JeremySavonet/Eurobot-2016_The-beach-bots/meca/10 telemetre laser/10.04 supp miroir.SLDPRT

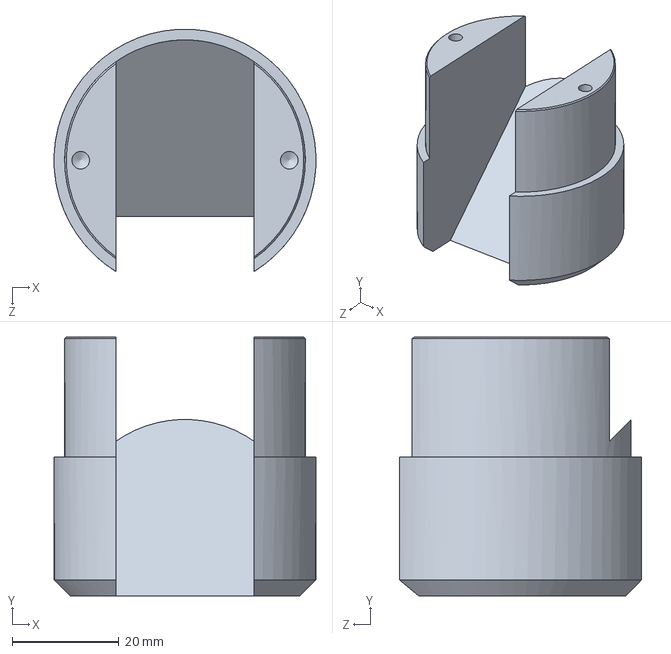
[picture p28: CAD file, 2015-11-07]
meca/10 telemetre laser/10.04 supp miroir.SLDPRT
49.0 x 48.4 x 45.3 mm
