JeremySavonet/Eurobot-2016_The-beach-bots/meca/12 bras/12.33 rot pince.SLDPRT

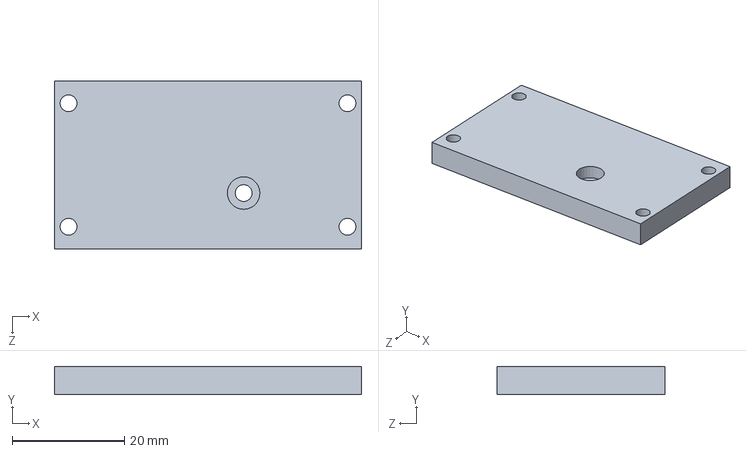
[picture p29: CAD file, 2015-11-07]
meca/12 bras/12.33 rot pince.SLDPRT
54.7 x 5.00 x 30.0 mm
