JeremySavonet/Eurobot-2016_The-beach-bots/meca/10 telemetre laser/10.06 poulie entrainement telemetre.SLDPRT

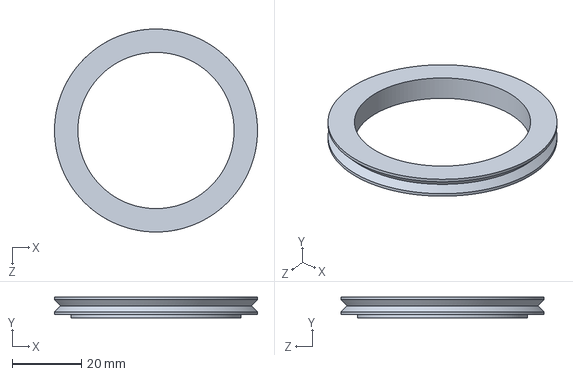
[picture p30: CAD file, 2015-11-07]
meca/10 telemetre laser/10.06 poulie entrainement telemetre.SLDPRT
58.5 x 6.00 x 58.5 mm
