JeremySavonet/Eurobot-2016_The-beach-bots/meca/22.01 telemetre.SLDPRT

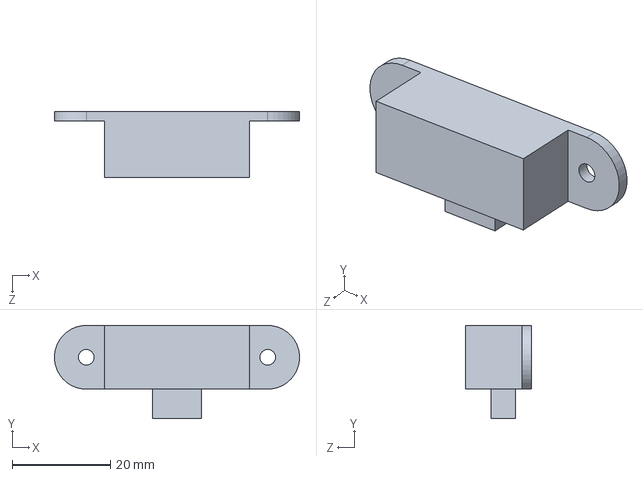
[picture p32: CAD file, 2015-11-07]
meca/22.01 telemetre.SLDPRT
50.0 x 19.0 x 13.5 mm
