JeremySavonet/Eurobot-2016_The-beach-bots/meca/04.02 supp servo telemetres.SLDPRT

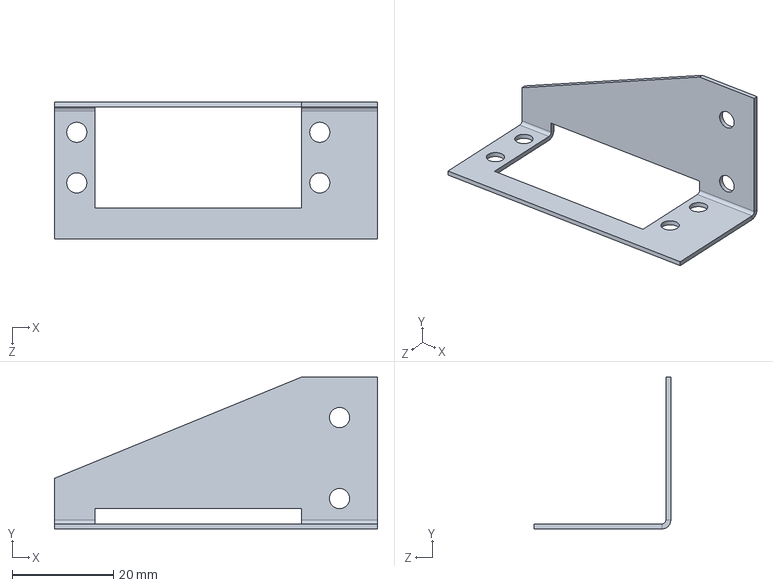
[picture p33: CAD file, 2015-11-07]
meca/04.02 supp servo telemetres.SLDPRT
63.8 x 30.0 x 27.0 mm
