JeremySavonet/Eurobot-2016_The-beach-bots/meca/10 telemetre laser/10.02 supp vertical telemetre.SLDPRT

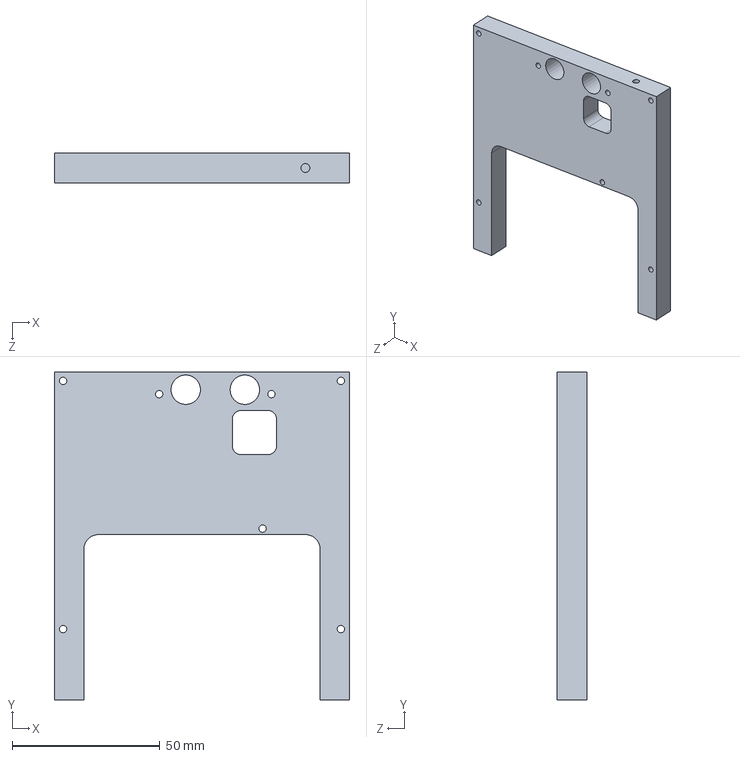
[picture p34: CAD file, 2015-11-07]
meca/10 telemetre laser/10.02 supp vertical telemetre.SLDPRT
100.0 x 111.0 x 10.0 mm
