JeremySavonet/Eurobot-2016_The-beach-bots/meca/04.01 supp telemetres.SLDPRT

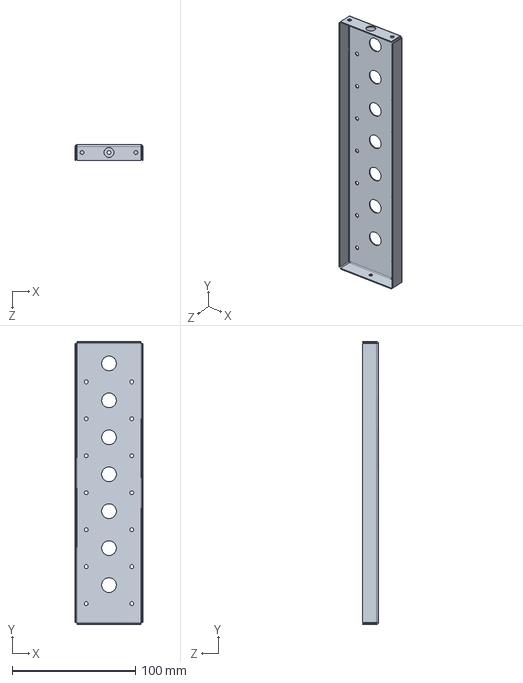
[picture p36: CAD file, 2015-11-07]
meca/04.01 supp telemetres.SLDPRT
55.0 x 229.8 x 12.8 mm
