JeremySavonet/Eurobot-2016_The-beach-bots/meca/10 telemetre laser/10.01 supp dessous telemetre.SLDPRT

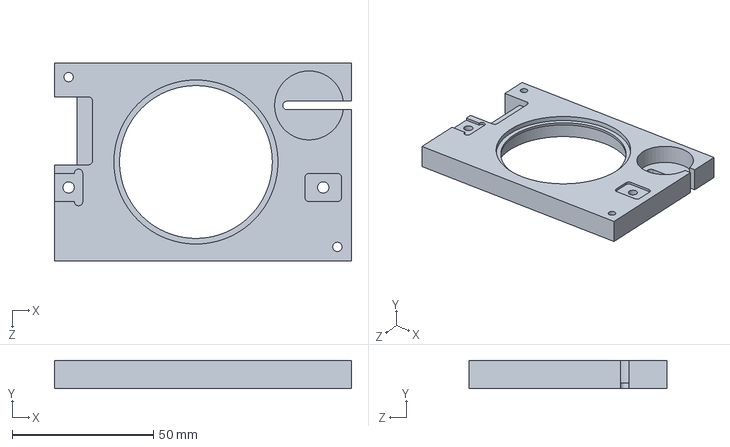
[picture p37: CAD file, 2015-11-07]
meca/10 telemetre laser/10.01 supp dessous telemetre.SLDPRT
105.0 x 10.0 x 70.0 mm
