JeremySavonet/Eurobot-2016_The-beach-bots/meca/12 bras/servo moteur MG995.SLDPRT

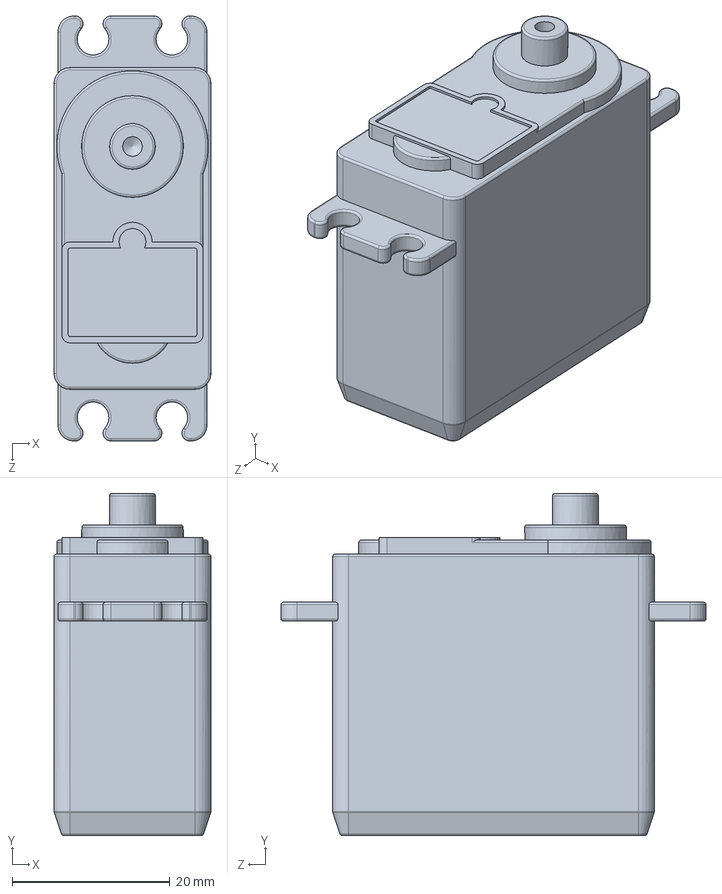
[picture p38: CAD file, 2015-11-07]
meca/12 bras/servo moteur MG995.SLDPRT
19.9 x 43.4 x 53.9 mm
