JeremySavonet/Eurobot-2016_The-beach-bots/meca/12 bras/vis - chcm4 - 39.sldprt

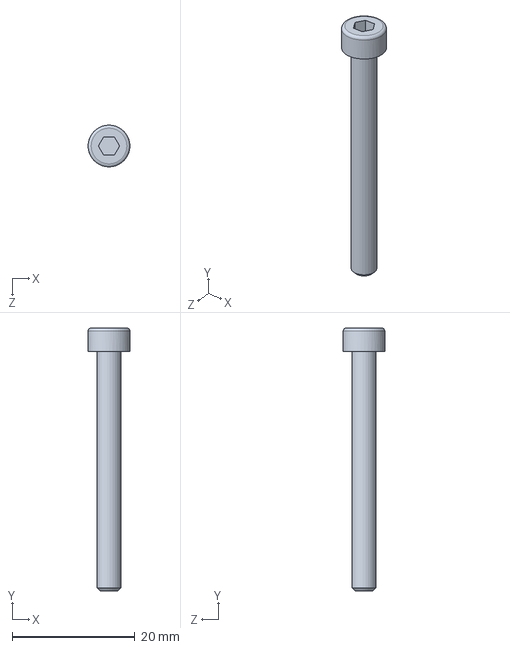
[picture p39: CAD file, 2015-11-07]
meca/12 bras/vis - chcm4 - 39.sldprt
6.80 x 42.8 x 6.80 mm
