JeremySavonet/Eurobot-2016_The-beach-bots/meca/03.04 supp codeurs.SLDPRT

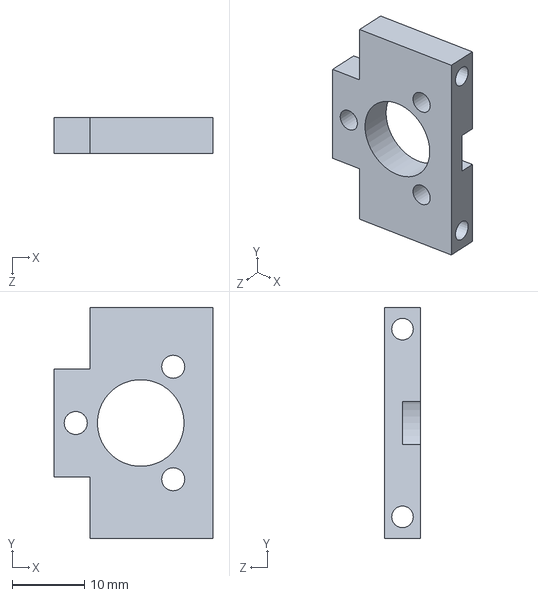
[picture p40: CAD file, 2015-11-07]
meca/03.04 supp codeurs.SLDPRT
22.0 x 32.0 x 5.00 mm
