JeremySavonet/Eurobot-2016_The-beach-bots/meca/10 telemetre laser/10.13 fentes led.SLDPRT

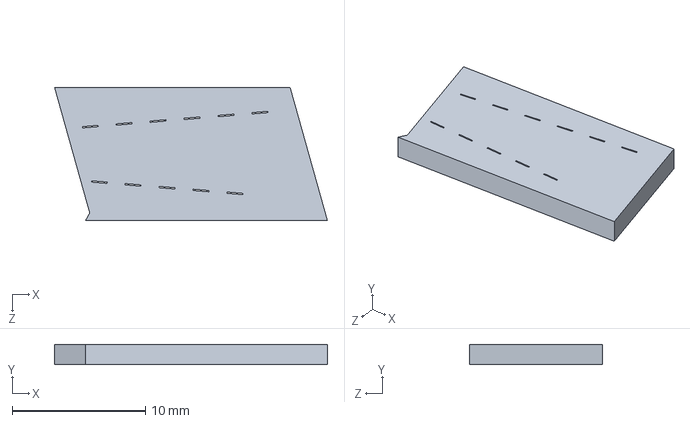
[picture p41: CAD file, 2015-11-07]
meca/10 telemetre laser/10.13 fentes led.SLDPRT
20.5 x 1.50 x 10.0 mm
