JeremySavonet/Eurobot-2016_The-beach-bots/meca/12 bras/12.12 rot bras.SLDPRT

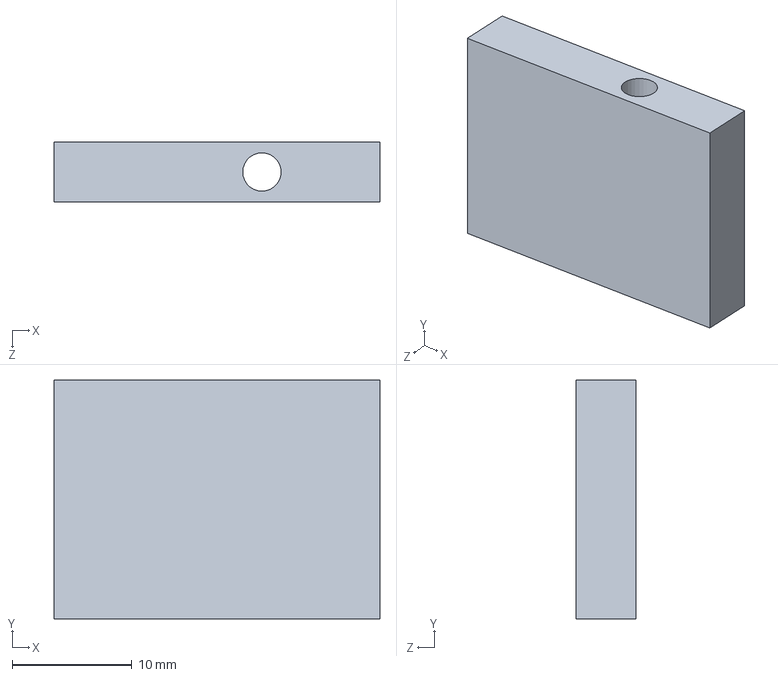
[picture p42: CAD file, 2015-11-07]
meca/12 bras/12.12 rot bras.SLDPRT
27.2 x 19.9 x 5.00 mm
