JeremySavonet/Eurobot-2016_The-beach-bots/meca/10 telemetre laser/10.03 supp fourche optique.SLDPRT

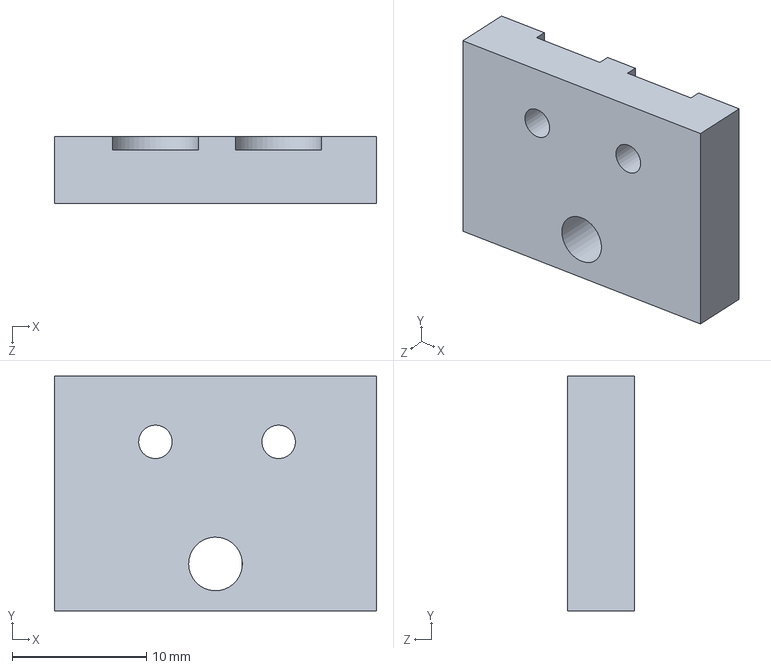
[picture p43: CAD file, 2015-11-07]
meca/10 telemetre laser/10.03 supp fourche optique.SLDPRT
24.0 x 17.5 x 5.00 mm
