JeremySavonet/Eurobot-2016_The-beach-bots/meca/12 bras/12.51 pince.SLDPRT

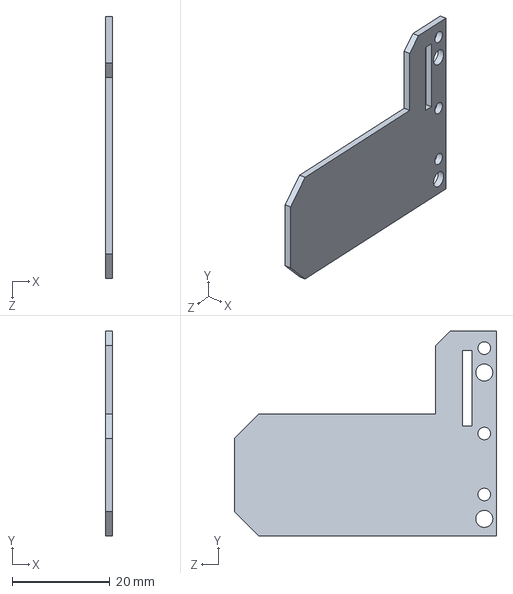
[picture p44: CAD file, 2015-11-07]
meca/12 bras/12.51 pince.SLDPRT
1.50 x 42.0 x 53.7 mm
