JeremySavonet/Eurobot-2016_The-beach-bots/meca/21.04 int coupe tout.SLDPRT

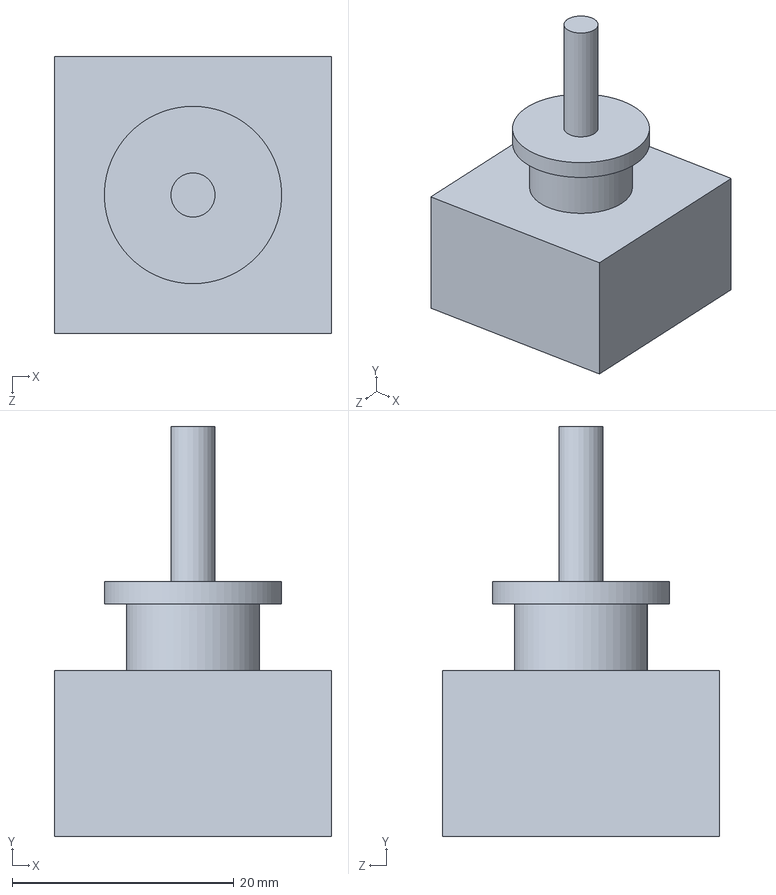
[picture p45: CAD file, 2015-11-07]
meca/21.04 int coupe tout.SLDPRT
25.0 x 37.0 x 25.0 mm
