JeremySavonet/Eurobot-2016_The-beach-bots/meca/03.01 codeurs.SLDPRT

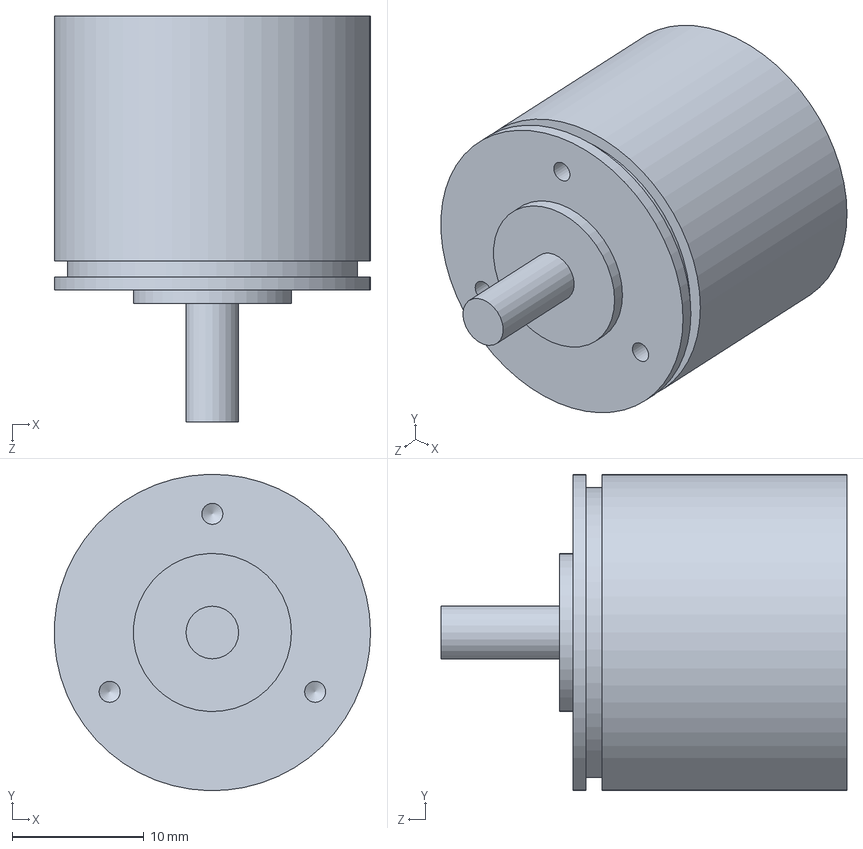
[picture p46: CAD file, 2015-11-07]
meca/03.01 codeurs.SLDPRT
24.0 x 24.0 x 30.8 mm
