JeremySavonet/Eurobot-2016_The-beach-bots/meca/10 telemetre laser/10.00 telemetre laser.SLDPRT

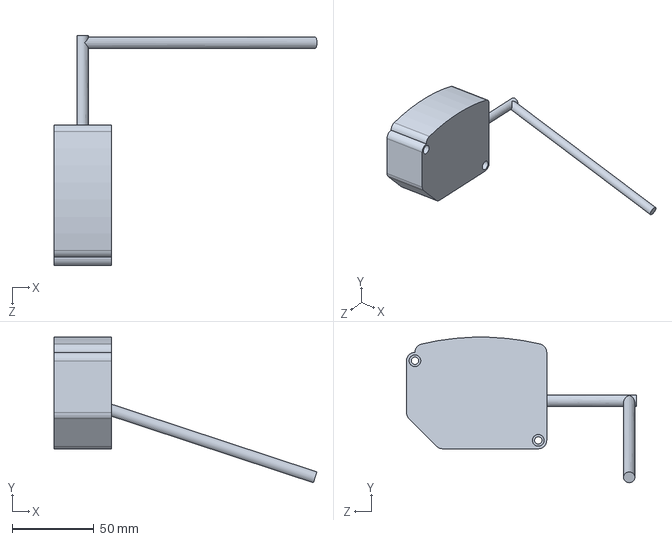
[picture p47: CAD file, 2015-11-07]
meca/10 telemetre laser/10.00 telemetre laser.SLDPRT
161.2 x 89.2 x 141.0 mm
