JeremySavonet/Eurobot-2016_The-beach-bots/meca/12 bras/12.34 rot pince.SLDPRT

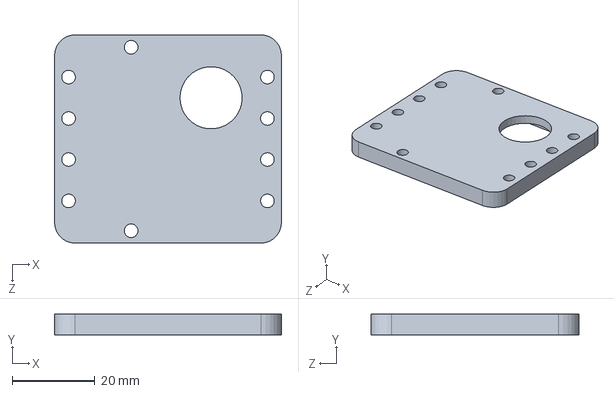
[picture p48: CAD file, 2015-11-07]
meca/12 bras/12.34 rot pince.SLDPRT
54.8 x 5.00 x 50.3 mm
