JeremySavonet/Eurobot-2016_The-beach-bots/meca/10 telemetre laser/10.00 fourche optique.SLDPRT

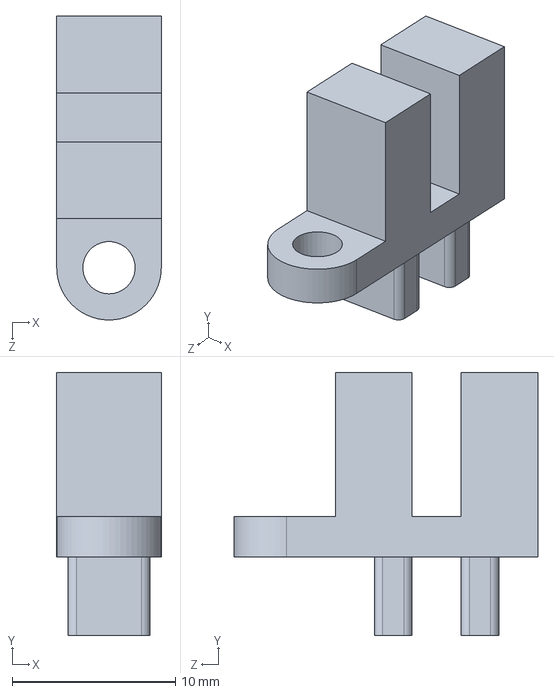
[picture p49: CAD file, 2015-11-07]
meca/10 telemetre laser/10.00 fourche optique.SLDPRT
6.40 x 16.1 x 18.6 mm
