JeremySavonet/Eurobot-2016_The-beach-bots/meca/12 bras/12.63 sup mors.SLDPRT

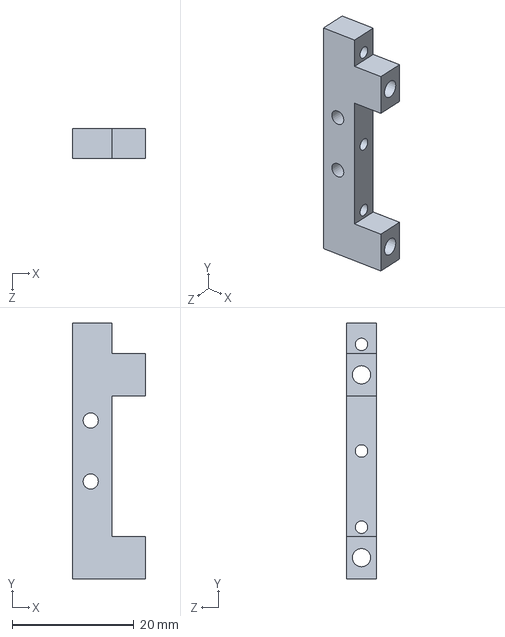
[picture p50: CAD file, 2015-11-07]
meca/12 bras/12.63 sup mors.SLDPRT
12.0 x 42.0 x 5.00 mm
