JeremySavonet/Eurobot-2016_The-beach-bots/meca/21.05 tirette.SLDPRT

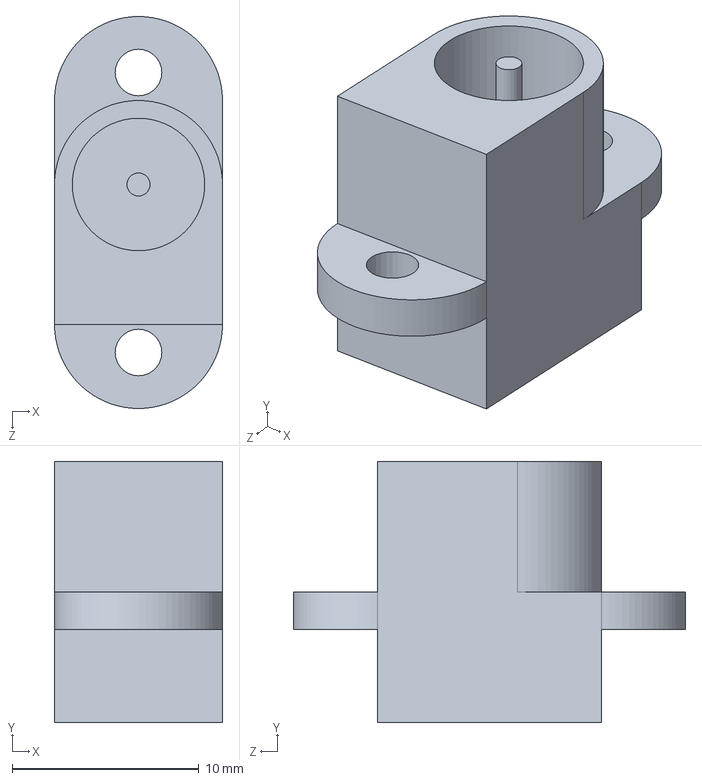
[picture p51: CAD file, 2015-11-07]
meca/21.05 tirette.SLDPRT
9.00 x 14.0 x 21.0 mm
