JeremySavonet/Eurobot-2016_The-beach-bots/meca/10 telemetre laser/10.00 roulement miroir.SLDPRT

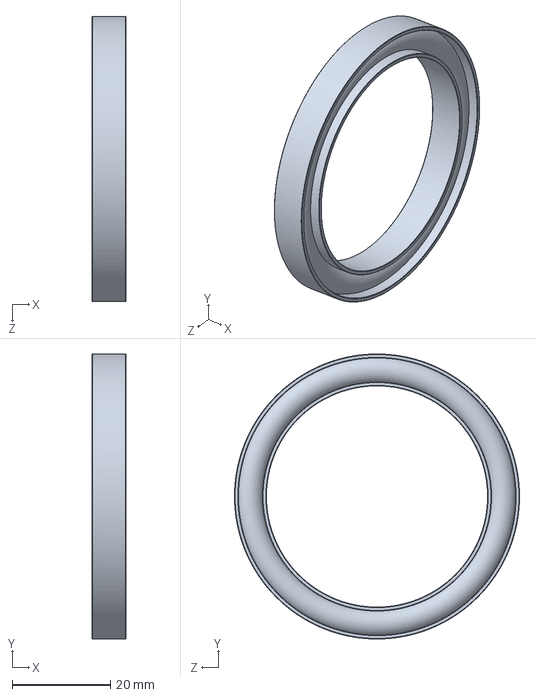
[picture p52: CAD file, 2015-11-07]
meca/10 telemetre laser/10.00 roulement miroir.SLDPRT
7.00 x 58.0 x 58.0 mm
