JeremySavonet/Eurobot-2016_The-beach-bots/meca/12 bras/12.25 bras 2.SLDPRT

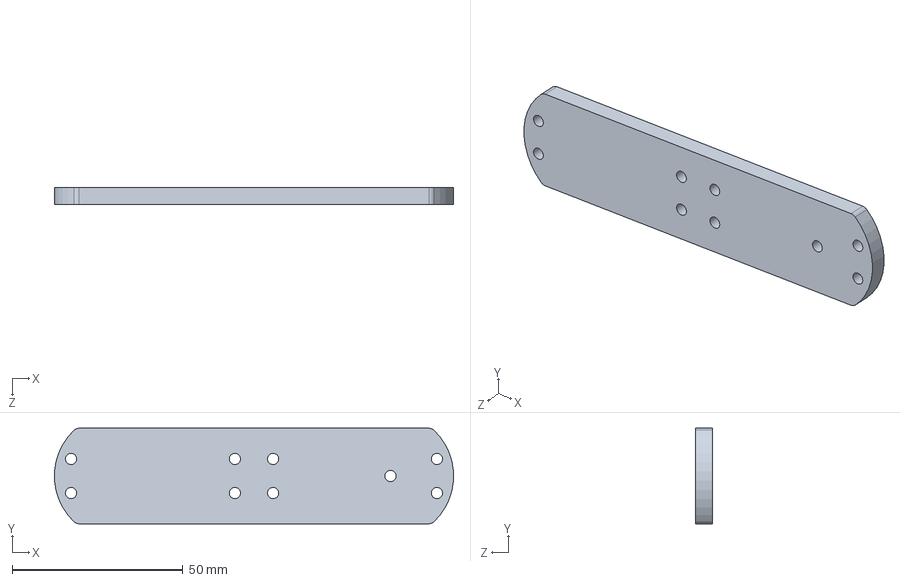
[picture p53: CAD file, 2015-11-07]
meca/12 bras/12.25 bras 2.SLDPRT
116.9 x 28.0 x 5.00 mm
