JeremySavonet/Eurobot-2016_The-beach-bots/meca/21.02 arret urgence.SLDPRT

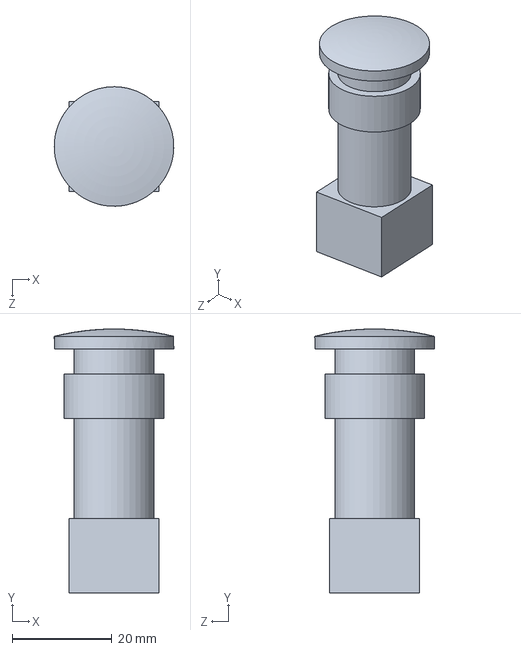
[picture p54: CAD file, 2015-11-07]
meca/21.02 arret urgence.SLDPRT
24.0 x 53.0 x 24.0 mm
