JeremySavonet/Eurobot-2016_The-beach-bots/meca/03.02 roue codeuse.SLDPRT

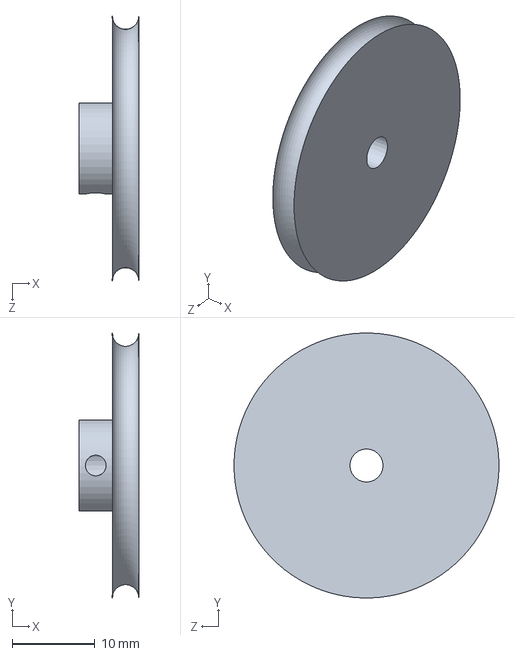
[picture p55: CAD file, 2015-11-07]
meca/03.02 roue codeuse.SLDPRT
7.20 x 32.0 x 32.0 mm
