JeremySavonet/Eurobot-2016_The-beach-bots/meca/12 bras/12.51 pince bielette.SLDPRT

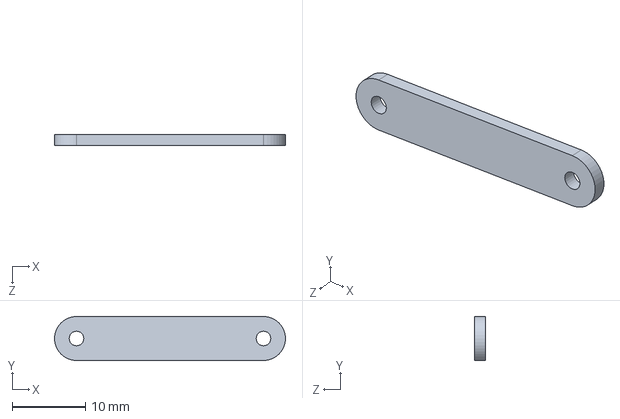
[picture p56: CAD file, 2015-11-07]
meca/12 bras/12.51 pince bielette.SLDPRT
31.5 x 6.00 x 1.50 mm
