JeremySavonet/Eurobot-2016_The-beach-bots/meca/01.01 chassis.SLDPRT

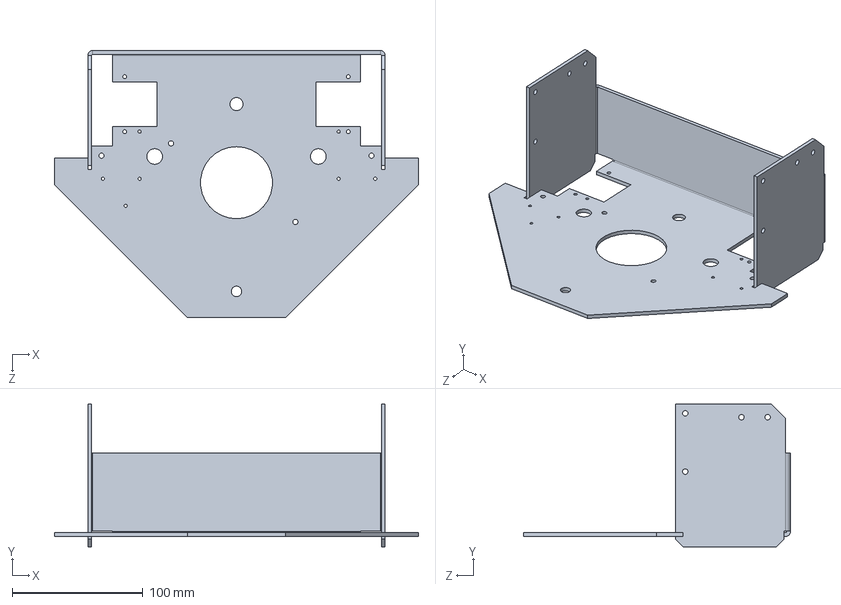
[picture p57: CAD file, 2015-11-07]
meca/01.01 chassis.SLDPRT
278.0 x 109.0 x 204.0 mm
