JeremySavonet/Eurobot-2016_The-beach-bots/meca/12 bras/12.61 tige.SLDPRT

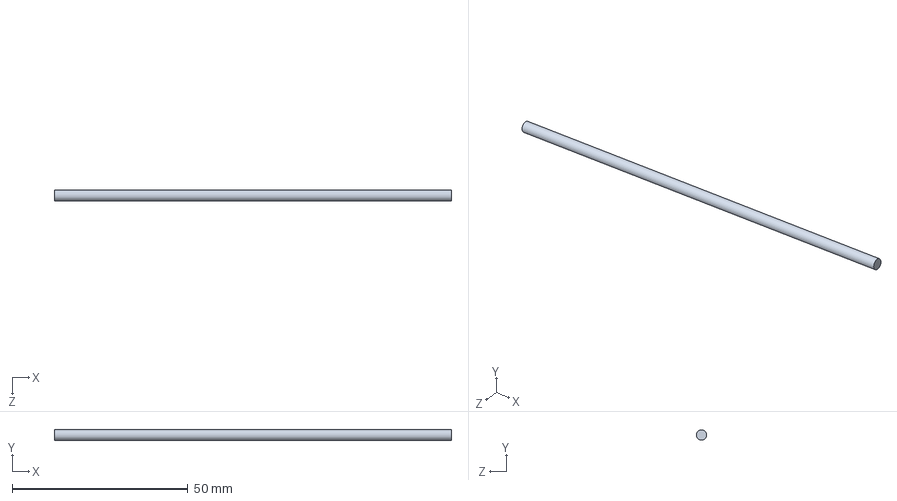
[picture p58: CAD file, 2015-11-07]
meca/12 bras/12.61 tige.SLDPRT
113.0 x 3.00 x 3.00 mm
