JeremySavonet/Eurobot-2016_The-beach-bots/meca/03.03 joint roue codeuse.SLDPRT

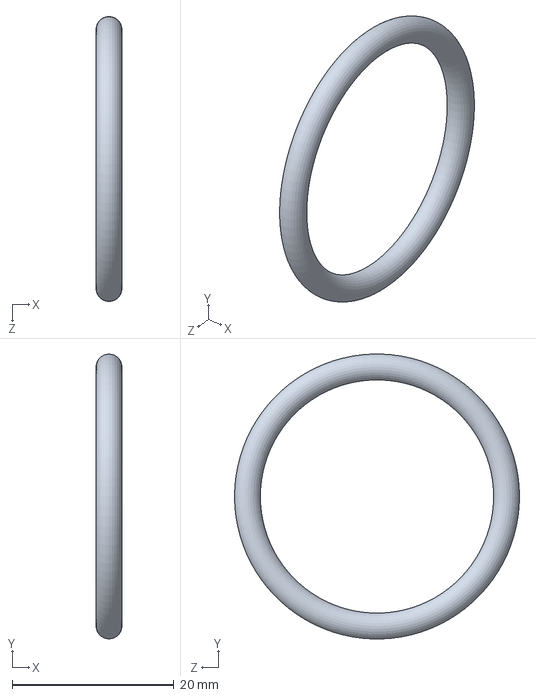
[picture p59: CAD file, 2015-11-07]
meca/03.03 joint roue codeuse.SLDPRT
3.20 x 35.2 x 35.2 mm
