JeremySavonet/Eurobot-2016_The-beach-bots/meca/12 bras/12.14 rot bras.SLDPRT

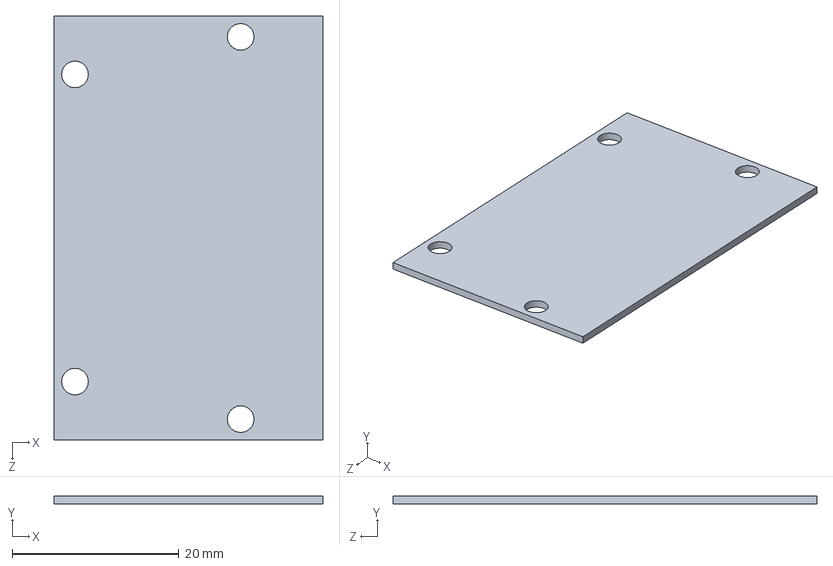
[picture p60: CAD file, 2015-11-07]
meca/12 bras/12.14 rot bras.SLDPRT
32.2 x 1.00 x 50.8 mm
