JeremySavonet/Eurobot-2016_The-beach-bots/meca/02.02 roue folle.SLDPRT

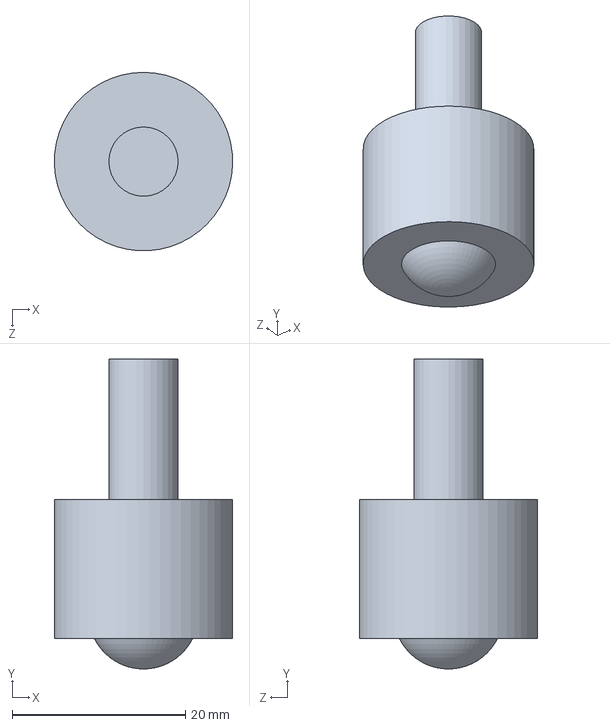
[picture p61: CAD file, 2015-11-07]
meca/02.02 roue folle.SLDPRT
20.6 x 35.8 x 20.6 mm
