JeremySavonet/Eurobot-2016_The-beach-bots/meca/12 bras/12.52 pince pile.SLDPRT

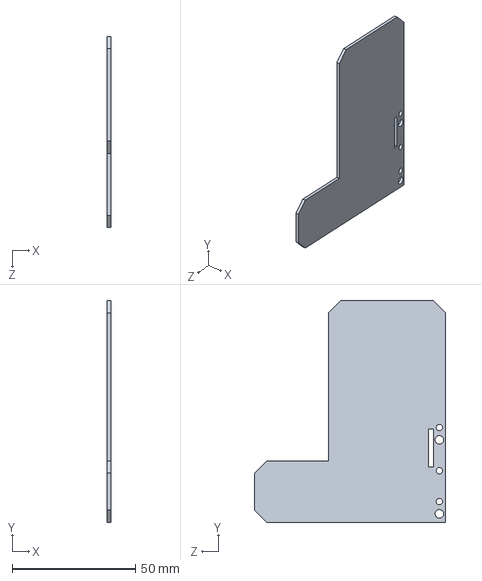
[picture p62: CAD file, 2015-11-07]
meca/12 bras/12.52 pince pile.SLDPRT
1.50 x 90.0 x 77.5 mm
