JeremySavonet/Eurobot-2016_The-beach-bots/meca/12 bras/vis - chcm3 - 6.sldprt

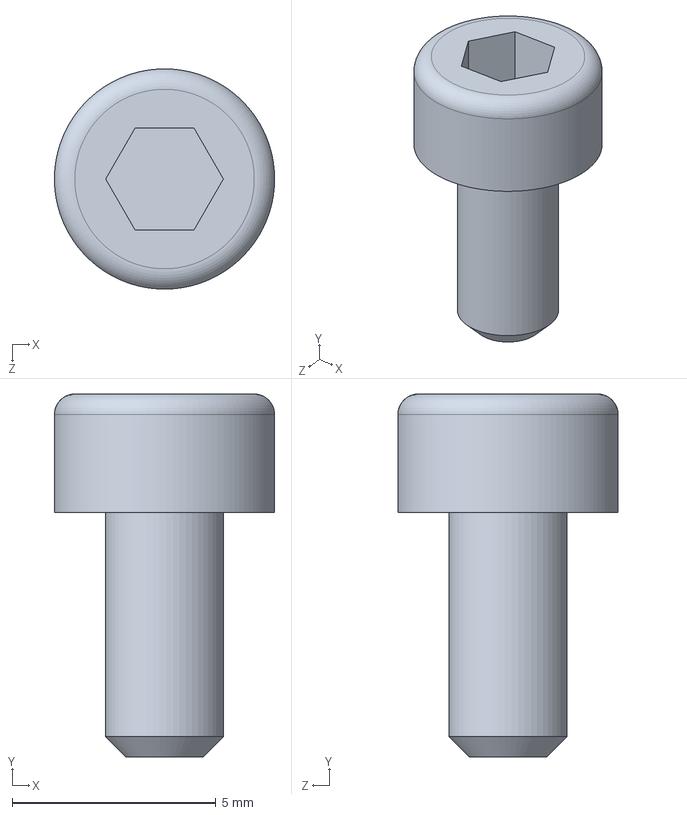
[picture p63: CAD file, 2015-11-07]
meca/12 bras/vis - chcm3 - 6.sldprt
5.40 x 8.90 x 5.40 mm
