JeremySavonet/Eurobot-2016_The-beach-bots/meca/12 bras/12.31 sup pince .SLDPRT

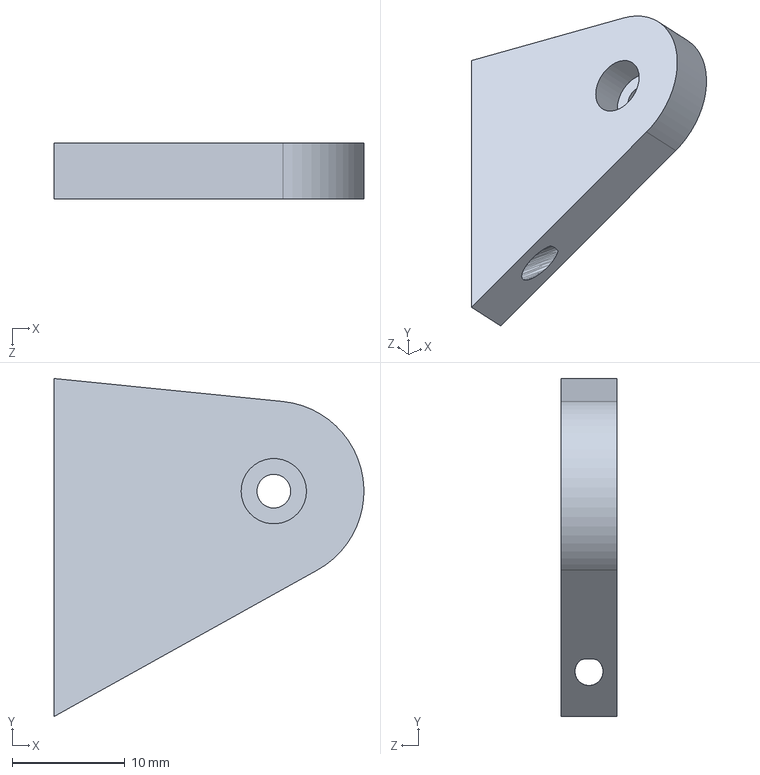
[picture p64: CAD file, 2015-11-07]
meca/12 bras/12.31 sup pince .SLDPRT
27.5 x 30.0 x 5.00 mm
