JeremySavonet/Eurobot-2016_The-beach-bots/meca/12 bras/12.21 bras 1.SLDPRT

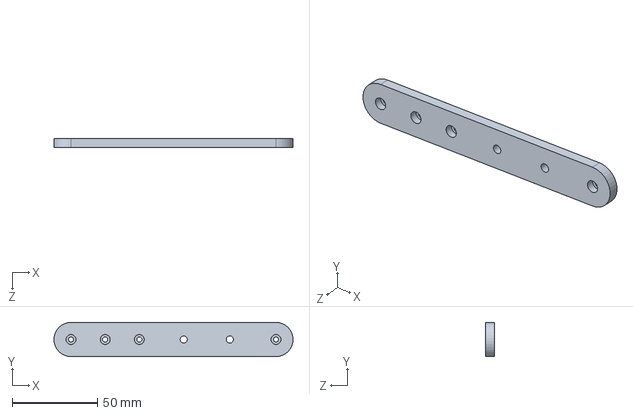
[picture p65: CAD file, 2015-11-07]
meca/12 bras/12.21 bras 1.SLDPRT
139.9 x 20.0 x 5.00 mm
