JeremySavonet/Eurobot-2016_The-beach-bots/meca/12 bras/vis - chcm4 - 13.sldprt

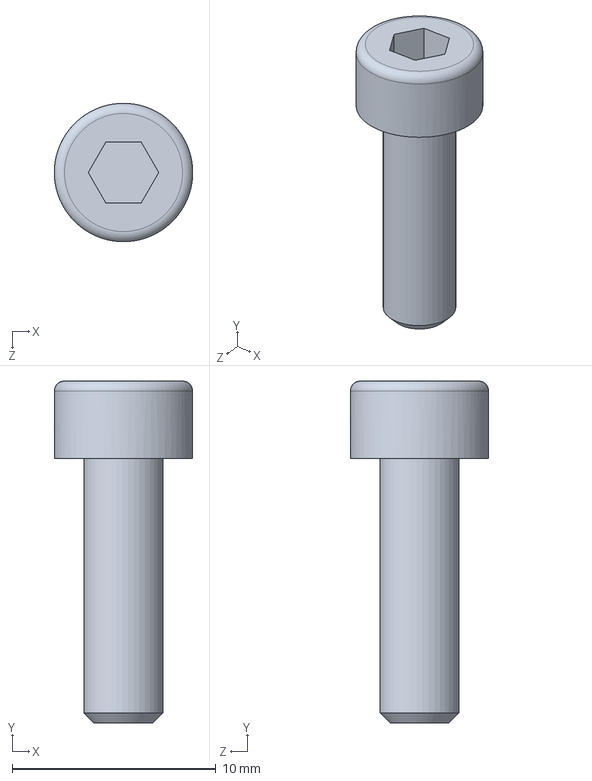
[picture p66: CAD file, 2015-11-07]
meca/12 bras/vis - chcm4 - 13.sldprt
6.80 x 16.8 x 6.80 mm
