JeremySavonet/Eurobot-2016_The-beach-bots/meca/12 bras/12.23 bras 1.SLDPRT

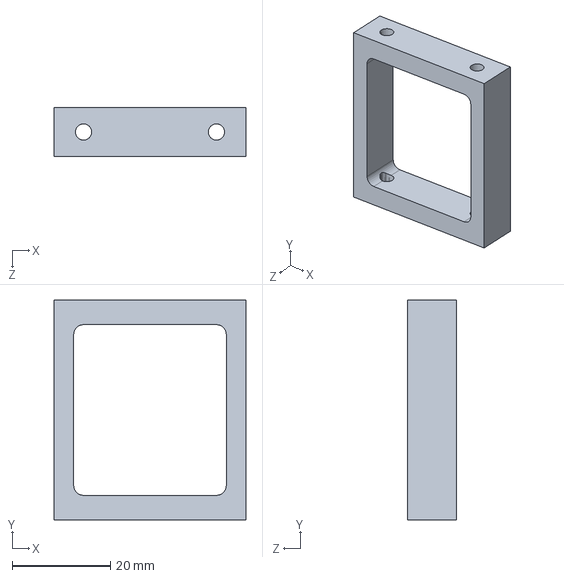
[picture p67: CAD file, 2015-11-07]
meca/12 bras/12.23 bras 1.SLDPRT
39.0 x 44.7 x 10.0 mm
