JeremySavonet/Eurobot-2016_The-beach-bots/meca/12 bras/vis - shs4 - 5.sldprt

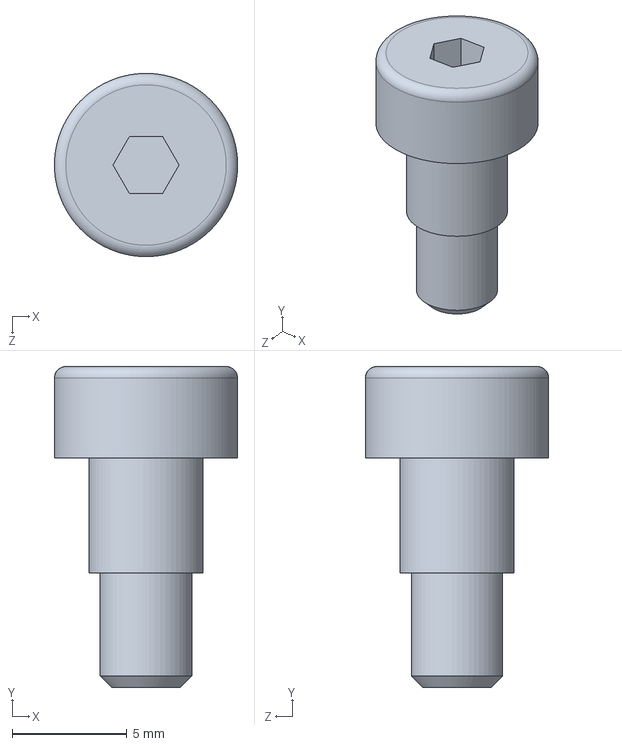
[picture p68: CAD file, 2015-11-07]
meca/12 bras/vis - shs4 - 5.sldprt
8.00 x 14.0 x 8.00 mm
