JeremySavonet/Eurobot-2016_The-beach-bots/meca/12 bras/12.11 rot bras.SLDPRT

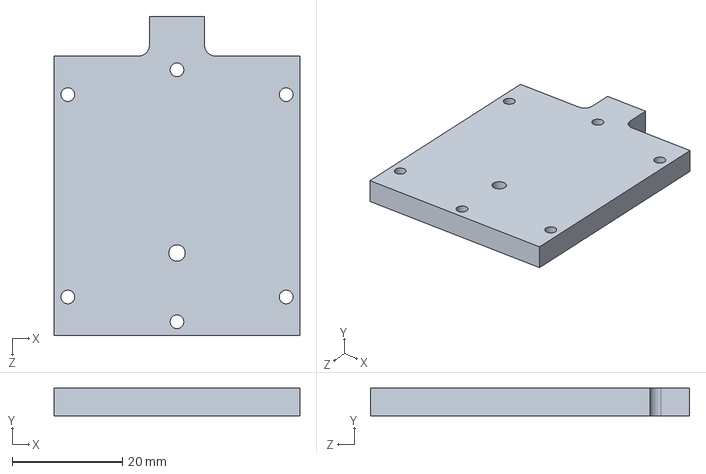
[picture p69: CAD file, 2015-11-07]
meca/12 bras/12.11 rot bras.SLDPRT
44.7 x 5.00 x 58.0 mm
