JeremySavonet/Eurobot-2016_The-beach-bots/meca/12 bras/12.13 rot bras.SLDPRT

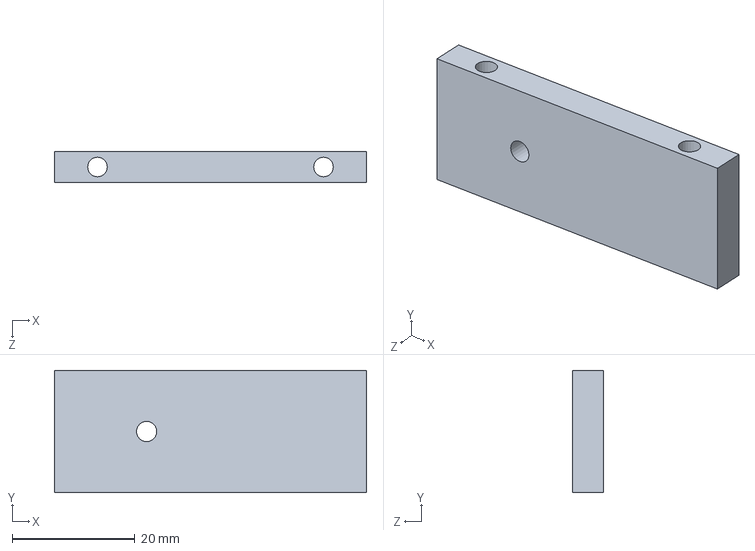
[picture p70: CAD file, 2015-11-07]
meca/12 bras/12.13 rot bras.SLDPRT
50.8 x 19.9 x 5.00 mm
