JeremySavonet/Eurobot-2016_The-beach-bots/meca/12 bras/12.01 base.SLDPRT

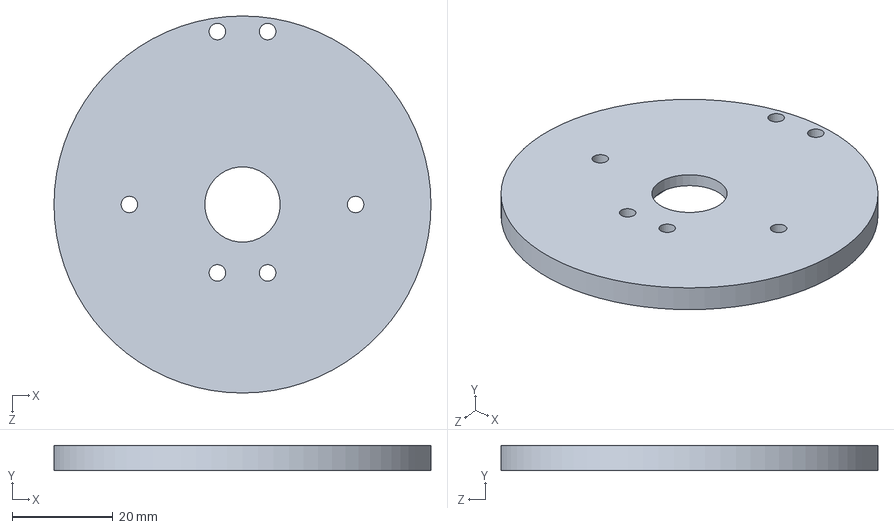
[picture p71: CAD file, 2015-11-07]
meca/12 bras/12.01 base.SLDPRT
75.0 x 5.00 x 75.0 mm
