JeremySavonet/Eurobot-2016_The-beach-bots/sw/MainBoard/modules/robot/position_manager/position_manager.h

/*  
 *  Copyright Droids Corporation, Microb Technology, Eirbot (2005)
 * 
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
 *  Revision : $Id: position_manager.h,v 1.5.4.4 2009-05-18 12:27:26 zer0 Exp $
 *
 */

#include "../../../common/math/vect2.h"

#include "../robot_system/robot_system.h"


#ifndef _ROBOT_POSITION_MANAGER_H_
#define _ROBOT_POSITION_MANAGER_H_

/*
 * This module manages the encoders to compute the robot's position. 
 * Enables centrifugal force compensation.
 *
 * A vehicle moving on a trajectory is subject to the centrifugal force F. This
 * force pulls the vehicle inside his own trajectory, which causes position
 * error who standard odometry systems do not account for.
 * This software includes a method to compensaite such errors. The main idea
 * is that since F is orthogonal to the speed vector, we suppose that the
 * lateral displacement will be pureley proportionnal to this force.
 *
 * The centrifugal force can be written as 
 *
 * \f$\begin{array}{lcl}
 * F &=&\frac{v^2}{R}\cdot m \\
 *   &=& M \cdot \omega^2 \cdot R\\
 *   &=& M \cdot V \cdot \omega\end{array}\f$
 *
 * The third form is the most interseting one because it does not require
 * the computation of the radius R. At any given point n of the trajectory
 * we can easily compute 
 *
 * \f$\begin{array}{ĺcl}
 * V_n &=& D_n - D_{n-1}\\
 * \omega_n &=& \theta_n - \theta_{n-1}
 * \end{array}\f$
 *
 * Lets write :
 *
 * \f$\begin{array}{lcl}
 * \Delta X &=& V_n \cos\theta_n\\
 * \Delta Y &=& V_n \sin\theta_n
 * \end{array} \f$
 *
 * In a classic odometry implementation, the equations of odometry are :
 * 
 * \f$\begin{array}{lcl}
 * X_{n+1} &=& X_n + \Delta X \\
 * Y_{n+1} &=& Y_n + \Delta Y 
 * \end{array} \f$
 *
 * In the modified implementation we have :
 *
 * \f$\begin{array}{lccccc}
 * X_{n+1} &=& X_n &+& \Delta X  &-& k \omega_n\ \Delta Y\\
 * Y_{n+1} &=& Y_n &+& \Delta Y  &+& k \omega_n\ \Delta X
 * \end{array} \f$
 *
 * K is found by experience, and given to the system using 
 * position_set_centrifugal_coef(). 
 *
 * \todo For now the code does not use the algorithm written above but another
 * equivalent, slower implementation.
 * */ 
#define CONFIG_MODULE_COMPENSATE_CENTRIFUGAL_FORCE

/*
 * Stores the physical dimensions of the robot.
 *
 * This structure stores the number of encoder impulsion per mm and the
 * distance between the wheels of the robot.
 */
struct robot_physical_params 
{
    double track_mm;			//Track (distance between wheels) in mm
    double distance_imp_per_mm;	//Impulsions per mm
};


/*
 * Stores a cartesian position in double.
 *
 * This structure holds a position of the robot in the double precision format.
 */
struct xya_position 
{
    double x; //The X coordinate, in mm.
    double y; //The Y coordinate, in mm.
    double a; //The angle relative to the X axis, in radians.
};

/*
 * Stores a cartesian position in int.
 * 
 * Same as xya_position but in integers.
 * Note: The angle is stored in degrees.
 */
struct xya_position_s16
{
    int16_t x; // The X coordinate, in mm.
    int16_t y; // The Y coordinate, in mm. 
    int16_t a; // The angle relative to the X axis in degrees.
};

/*
 * Instance of the odometry subsystem.
 *
 * This structure holds everything that is needed to compute and store the
 * position of the robot.
 */
struct robot_position
{
    uint8_t use_ext;					// Only useful when we have 2 sets of encoders.
    struct robot_physical_params phys;	// The physical parameters of the robot.
    struct xya_position pos_d;			// Position of the robot in double.
    struct xya_position_s16 pos_s16;	// Position of the robot in integers.
    struct rs_polar prev_encoders;		// Previous state of the encoders.
    struct robot_system *rs;			// Robot system used for the computations.
	
#ifdef CONFIG_MODULE_COMPENSATE_CENTRIFUGAL_FORCE	
    double centrifugal_coef;			// Coefficient for the centrifugal computation
#endif
};

/*
 * Initialization of the odometry subsystem.
 *
 * This function initialize a robot_position structure, setting everything to 0.
 * [in] pos The odometry instance to initialize. 
 */
void position_init( struct robot_position *pos );

#ifdef CONFIG_MODULE_COMPENSATE_CENTRIFUGAL_FORCE	
/*
 * Set centrifugal coef.
 * 
 * This functions sets the centrifugal coef for the odometry compensation.
 * [in] pos The odometry instance.
 * [in] coef The centrifugal force coefficient.
 */
void position_set_centrifugal_coef( struct robot_position *pos, double coef );
#endif

/*
 * Set a new robot position.
 * [in] pos The odometry instance.
 * [in] x, y The new coordinate of the robot, in mm.
 * [in] a_deg The new angle of the robot, in degree.
 */
void position_set( struct robot_position *pos, 
                   int16_t x, 
                   int16_t y, 
                   double a_deg );

/*
 * Tells the robot to use the separate wheels encoders.
 *
 * If the robot has input for both motor encoders and separate wheel encoders,
 * the user can instruct the robot to use one or another encoder depending on
 * the situation.
 * [in] pos The odometry instance.
 * Note: By default the odometry system uses the separate wheel encoders.
 */
void position_use_ext( struct robot_position *pos );

/* Tells the robot to use the motor encoders.
 *
 * [in] pos The odometry instance.
 */
void position_use_mot( struct robot_position *pos );


/* Sets the physical parameters of the robot. 
 *  [in] pos The robot_position instance to configure.
 *  [in] track_mm The distance between the wheels, in mm.
 *  [in] distance_imp_per_mm The number of encoder pulses for one mm.
 */
void position_set_physical_params( struct robot_position *pos, 
                                   double track_mm,
                                   double distance_imp_per_mm );

/*
 * Set related robot_system structure.
 *
 * Save in pos structure the pointer to the associated robot_system. 
 * The robot_system structure is used to get values from virtual encoders
 * that return angle and distance.
 *
 * [in] pos The odometry system instance.
 * [in] rs The robot_system instance.
 */
void position_set_related_robot_system( struct robot_position *pos, 
                                        struct robot_system *rs );

/*
 * Updates the position.
 *
 * Process the absolute position (x,y,a) depending on the delta on
 * virtual encoders since last read, and depending on physical
 * parameters.
 *
 * [in] pos The odometry system instance.
 *
 * Note: This function should be called at a fixed interval to ensure good
 * results.
 */
void position_manage( struct robot_position *pos );


/*
 * Get current X. 
 *
 * [in] pos The odometry system instance.
 * Return Current x in mm in integer.
 */ 
int16_t position_get_x_s16( struct robot_position *pos );

/* 
 * Get current Y. 
 *
 * [in] pos The odometry system instance.
 * Return Current Y in mm in integer.
 */
int16_t position_get_y_s16( struct robot_position *pos );

/* 
 * Get current angle. 
 *
 * [in] pos The odometry system instance.
 * Return Current angle in degrees in integer.
 */
int16_t position_get_a_deg_s16( struct robot_position *pos );

/* 
 * Get current X. 
 *
 * [in] pos The odometry system instance.
 * Return Current x in mm in double.
 */ 
double position_get_x_double( struct robot_position *pos );

/* 
 * Get current X. 
 *
 * [in] pos The odometry system instance.
 * Return Current x in mm in float.
 */ 
float position_get_x_float( struct robot_position *pos );

/* 
 * Get current Y. 
 *
 * [in] pos The odometry system instance.
 * Return Current Y in mm in double.
 */ 
double position_get_y_double( struct robot_position *pos );

/* 
 * Get current Y. 
 *
 * [in] pos The odometry system instance.
 * Return Current Y in mm in float.
 */ 
float position_get_y_float( struct robot_position *pos );

/* 
 * Get current position
 * 
 * [in] pos The odometry system instance.
 * Returns current position stored in a vect2_cart.
 */
vect2_cart position_get_xy_vect( struct robot_position *pos );

/* 
 * Returns current angle.
 *
 * [in] pos The odometry system instance.
 * Returns Current angle in radians in double.
 */
double position_get_a_rad_double( struct robot_position *pos );

/*
 * Returns current angle.
 *
 * [in] pos The odometry system instance.
 * Returns Current angle in radians in float.
 */
float position_get_a_rad_float( struct robot_position *pos );

#endif // _POSITION_MANAGER_H_
