JeremySavonet/Eurobot-2016_The-beach-bots/sw/MainBoard/system.h

/*
 * Manage board structure here
 *
 * Author: Jeremy S.
 * Date: 2015-10-03
 * Version: V1.0
 */

#ifndef _SYSTEM_H_
#define _SYSTEM_H_

// For robot structure
#include "versatile_cs.h"

// For robot sensor modules
#include "modules/sensors/battery.h"
#include "modules/sensors/infrared.h"
#include "modules/sensors/temperature.h"

// Enum of state of the system
typedef enum
{
    SYSTEM_UNKNOWN,         // System is in unknown state
    SYSTEM_INITIALIZING,    // System is about to initialize
    SYSTEM_RUNNING,         // System is running
    SYSTEM_GAME_STARTED,    // System game started
    SYSTEM_CRASH,           // System is crashed
    SYSTEM_TERMINATING,     // System is about to stop
    SYSTEM_STOPPED          // System is stopped
} system_state_t;

typedef struct
{
    // Add here all sensor strctures
    battery_data_t batt_sensor;
    infrared_data_t ir_sensors;
    temperature_data_t temp_sensors;

} system_sensors_t;

typedef struct
{
    // Add here all comm structure ( can_proto, spi_proto, i2c_proto... )
} system_comm_t;

typedef struct
{
    /*
     * Contains the robot global variables:
     * - robot_sys
     * - encoders
     * - position_manager
     * - control_sys
     * - pid...
     *
     * This struct acts like a namespace for global variables.
     * They can be access by robot.color for example...
     */
    versatile_robot_t robot;

    /*
     * Contains the io variables:
     * - buttons
     * - led...
     */
    //versatile_io_t io;
} system_controls_t;

typedef struct
{
    // Aggregate here all robot structures
    system_state_t    sys_state;
    system_comm_t     comm;
    system_sensors_t  sensors;
    system_controls_t controls;

} system_t;

extern system_t sys;

void system_print_boot_msg( void );
void system_init( void );
void system_deinit( void );

#endif // _SYSTEM_H_
