JeremySavonet/Eurobot-2016_The-beach-bots/sw/MainBoard/comm/debug_manager.h

/*
 * Debug manager module
 * Author: Jeremy S.
 */

#ifndef _DEBUGMANAGER_H_
#define _DEBUGMANAGER_H_

#include <stdio.h>
#include <string.h>

#include "ch.h"
#include "chprintf.h"
#include "hal.h"
#include "test.h"

#include "usb_manager.h"

#define DEBUG
#define DLEVEL 3
#ifdef DEBUG
#define DPRINT( level, ... ) \
    do { \
        if( DLEVEL >= (level) ) \
            chprintf( (BaseSequentialStream * )&SD3, __VA_ARGS__); \
   } while (0)
#else
#define DPRINT( level, ... )
#endif

#define DEBUG
#define DLEVEL 3
#ifdef DEBUG
#define CLI_PRINT( level, ... ) \
    do { \
        if( DLEVEL >= (level) ) \
            chprintf( (BaseSequentialStream * )&SDU2, __VA_ARGS__); \
   } while (0)
#else
#define CLI_PRINT( level, ... )
#endif

void debug_manager_init( void );

#endif // _DEBUGMANAGER_H_
