JeremySavonet/Eurobot-2016_The-beach-bots/sw/MainBoard/strat_high_level.c

/*
 * Start high level commands.
 * Author: Jeremy S.
 * Rev: 1.0
 */

#include "strat_high_level.h"

// Setup arm position before the game. Ready for war...
void setup_arm_position( void )
{
    // TODO: implements
}
