JeremySavonet/Eurobot-2016_The-beach-bots/sw/MainBoard/strat_high_level.h

/*
 * Start high level commands.
 * Author: Jeremy S.
 * Rev: 1.0
 */

#ifndef _STRAT_HIGH_LEVEL_H
#define _STRAT_HIGH_LEVEL_H

// Fonction de callage
void prepare_for_war( void );
void setup_arm_position( void );

#endif // _STRAT_HIGH_LEVEL_H
